shlokdee/pico-drum/pico-drum_schematics/pico-drum_schematics.kicad_sch

## KiCad design pico-drum_schematics/pico-drum_schematics.kicad_sch (2026-09-18)

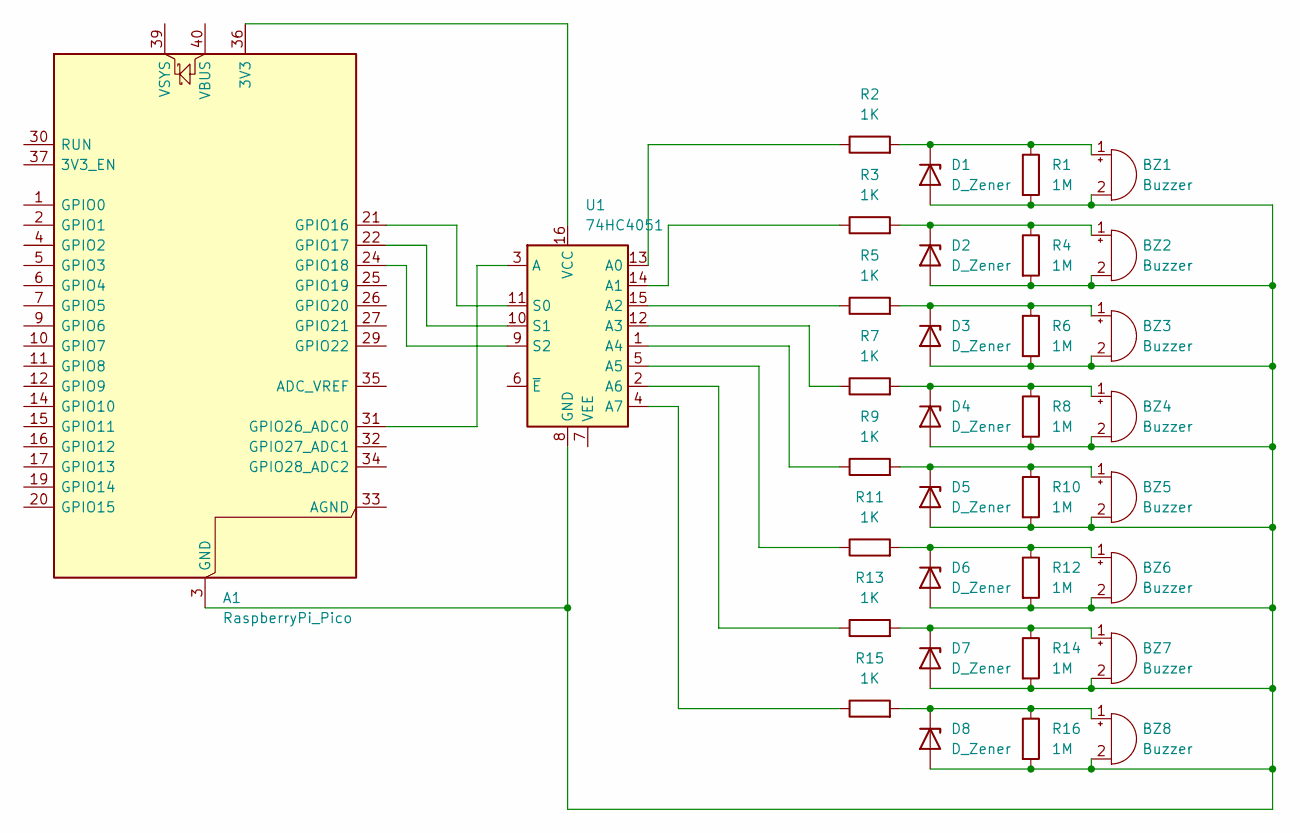
[picture p6: schematic pico-drum_schematics.kicad_sch]

Parts:
A1: RaspberryPi_Pico; RaspberryPi_Pico_Common_Unspecified
BZ1, BZ2, BZ3, BZ4, BZ5, BZ6, BZ7, BZ8: Buzzer; SOIC-8_3.9x4.9mm_P1.27mm
D1, D2, D3, D4, D5, D6, D7, D8: D_Zener; DIP-40_W15.24mm
R1, R4, R6, R8, R10, R12, R14, R16: 1M
R2, R3, R5, R7, R9, R11, R13, R15: 1K; DIP-8_W7.62mm
U1: 74HC4051; RaspberryPi_Pico_Common_Unspecified

Connections:
unnamed: A1.3 (GND), A1.8 (GND), A1.13 (GND), A1.18 (GND), A1.23 (GND), A1.28 (GND), A1.38 (GND), BZ1.2 (-), BZ2.2 (-), BZ3.2 (-), BZ4.2 (-), BZ5.2 (-), BZ6.2 (-), BZ7.2 (-), BZ8.2 (-), D1.2 (A), D2.2 (A), D3.2 (A), D4.2 (A), D5.2 (A), D6.2 (A), D7.2 (A), D8.2 (A), R1.2, R4.2, R6.2, R8.2, R10.2, R12.2, R14.2, R16.2, U1.8 (GND)
unnamed: A1.21 (GPIO16), U1.11 (S0)
unnamed: A1.22 (GPIO17), U1.10 (S1)
unnamed: A1.24 (GPIO18), U1.9 (S2)
unnamed: A1.31 (GPIO26_ADC0), U1.3 (A)
unnamed: A1.36 (3V3), U1.16 (VCC)
unnamed: BZ1.1 (+), D1.1 (K), R1.1, R2.2
unnamed: BZ2.1 (+), D2.1 (K), R3.2, R4.1
unnamed: BZ3.1 (+), D3.1 (K), R5.2, R6.1
unnamed: BZ4.1 (+), D4.1 (K), R7.2, R8.1
unnamed: BZ5.1 (+), D5.1 (K), R9.2, R10.1
unnamed: BZ6.1 (+), D6.1 (K), R11.2, R12.1
unnamed: BZ7.1 (+), D7.1 (K), R13.2, R14.1
unnamed: BZ8.1 (+), D8.1 (K), R15.2, R16.1
unnamed: R2.1, U1.13 (A0)
unnamed: R3.1, U1.14 (A1)
unnamed: R5.1, U1.15 (A2)
unnamed: R7.1, U1.12 (A3)
unnamed: R9.1, U1.1 (A4)
unnamed: R11.1, U1.5 (A5)
unnamed: R13.1, U1.2 (A6)
unnamed: R15.1, U1.4 (A7)
